kagjerde/Arduino-Macro-Ring/IMG_5001.JPG

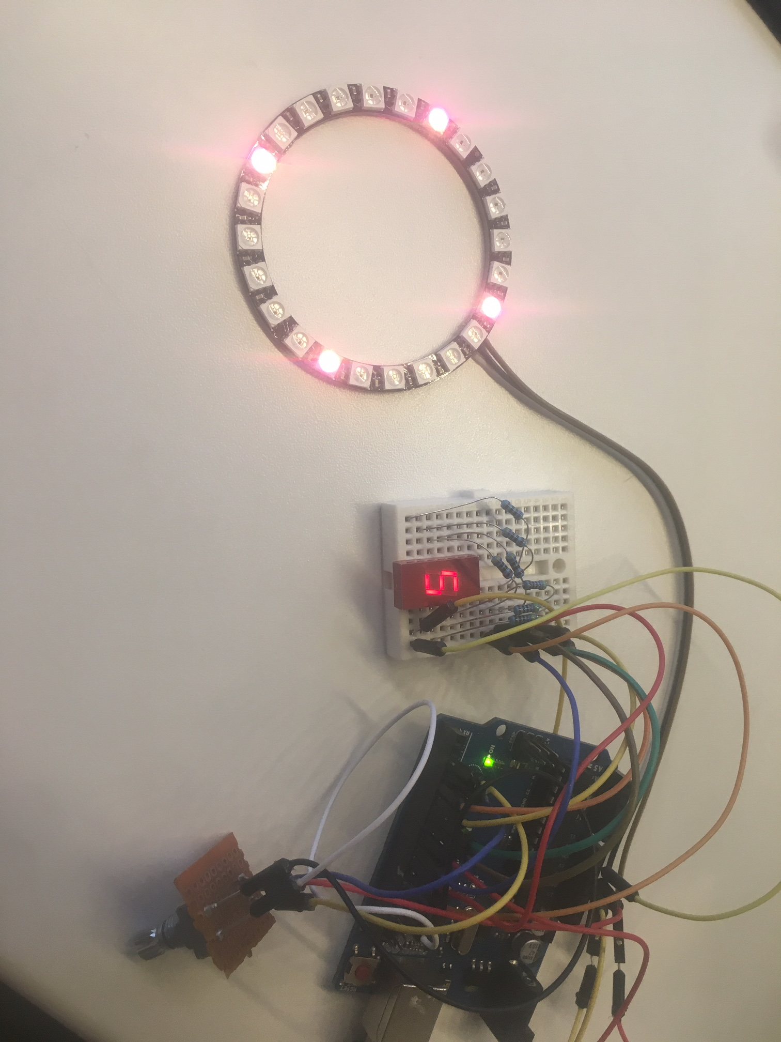
IMG_5001.JPG
