kagjerde/Arduino-Macro-Ring/IMG_5002.JPG

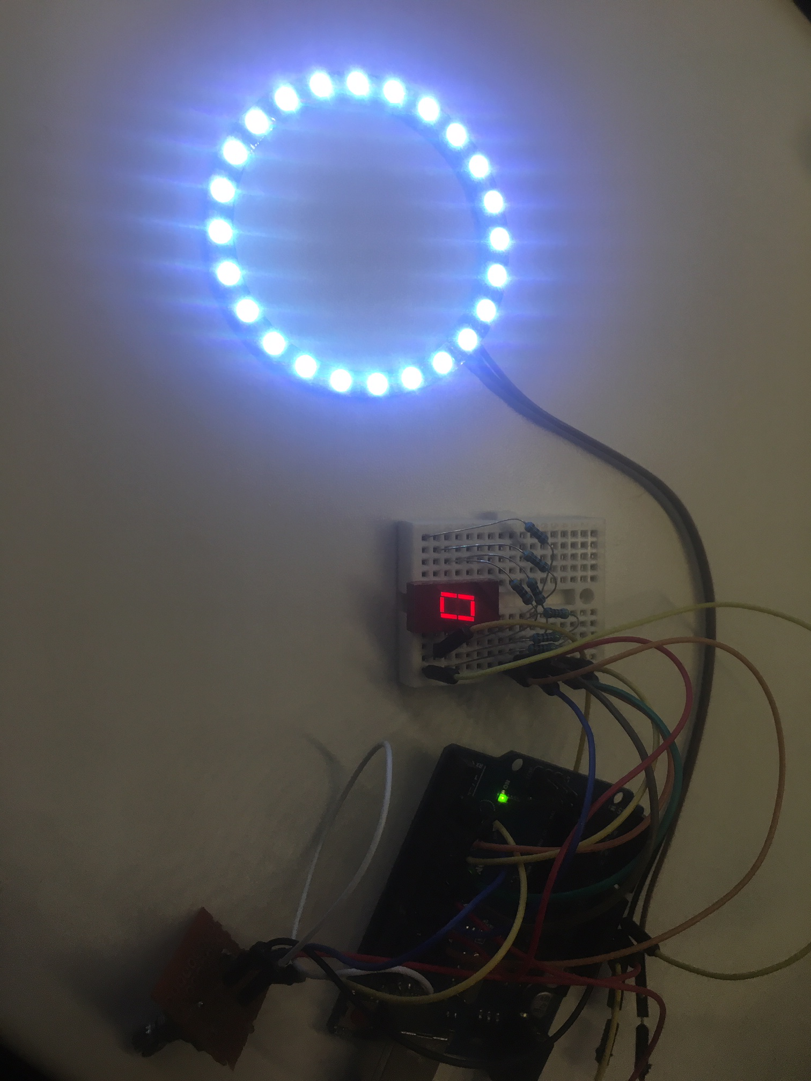
IMG_5002.JPG
