kagjerde/Arduino-Macro-Ring/IMG_5003.JPG

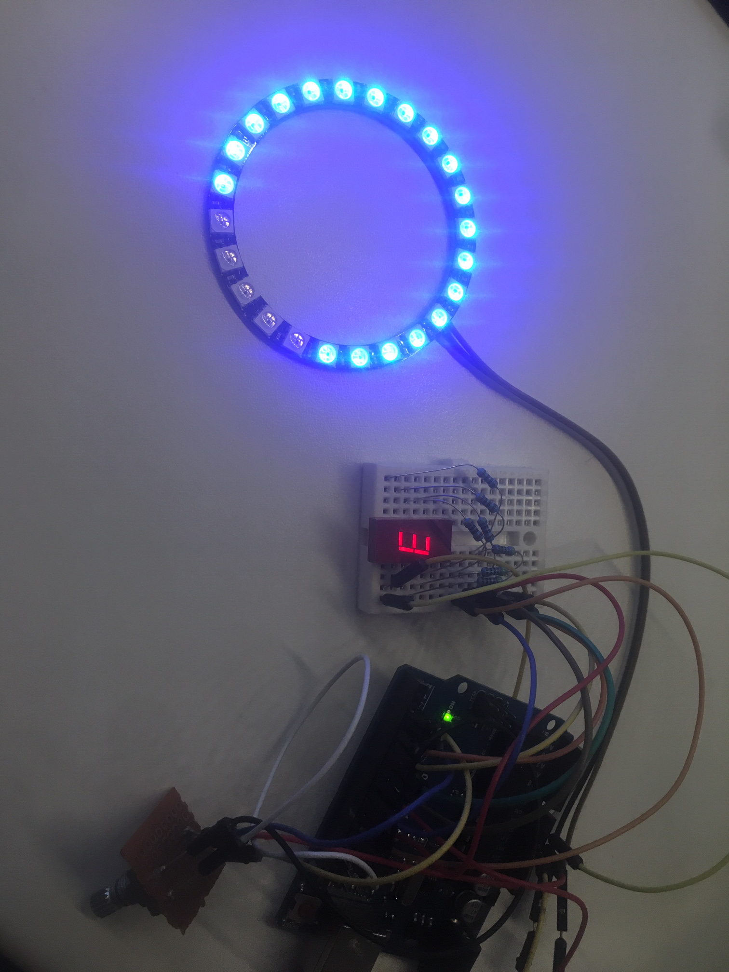
IMG_5003.JPG
